alexmorten/mini_lolly/firmware/src/led_config.cpp

#include "led_config.h"

float ledsMap[63][2] = {
    {-0.0985116422863797, 0.09024398783651263},
    {-0.514408391630448, 0.3578427989568794},
    {-0.7794920791843482, 0.3998480983729966},
    {-0.9467835928933912, 0.11779388593764692},
    {-0.7076017315349176, 0.18642805509545712},
    {-0.37047881056988474, 0.15291219695658648},
    {-0.5503713417943471, 0.02272098685415099},
    {-0.8200293214491392, -0.07612956202633989},
    {-1.0, -0.23035350960899287},
    {-0.8187364063954206, -0.38820440897308395},
    {-0.6363700436039336, -0.2030915871434229},
    {-0.263111440931452, -0.046545178884178265},
    {-0.4004067957620974, -0.23207035568267942},
    {-0.6067110617392961, -0.47000306465049035},
    {-0.6889436188701723, -0.6994117702571708},
    {-0.436305255852901, -0.9572074101907608},
    {-0.4554935411358794, -0.7240959848348449},
    {-0.38276672008746104, -0.4587592594437879},
    {-0.16290685469637636, -0.31368934272478505},
    {-0.23918741431827337, -0.6652427895260754},
    {-0.19616054331776836, -0.9143842576119163},
    {0.13960923150341062, -0.9989369148524919},
    {0.004029214556408834, -0.8015800157610744},
    {-0.06646284519518637, -0.51313790086828},
    {0.016519470081657397, -0.18821304184730073},
    {0.14068425793888042, -0.6250791331662742},
    {0.3082055374571858, -0.8308695872223051},
    {0.6245980254477382, -0.7334851047906785},
    {0.40237886948574564, -0.6256160136983848},
    {0.17908013689466154, -0.38264280293212366},
    {0.40180111215223974, -0.39978649851133796},
    {0.6646676469933895, -0.5042908271003209},
    {0.9005082870010603, -0.509898112801168},
    {0.8753019418320025, -0.2696794355065852},
    {0.6184366361690004, -0.2856530644251423},
    {0.2520625462048526, -0.1603342690559568},
    {0.4704660829487792, -0.10340424498338555},
    {0.7763548125138815, -0.06420996270680296},
    {0.9894878464255704, 0.05081788207788568},
    {0.9760781785624362, 0.4144010288956847},
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
};
